Ridhoandika112/SPIKO-Sistem-Pakan-Ikan-Otomatis/3D Desain/Tampak Jauh.png

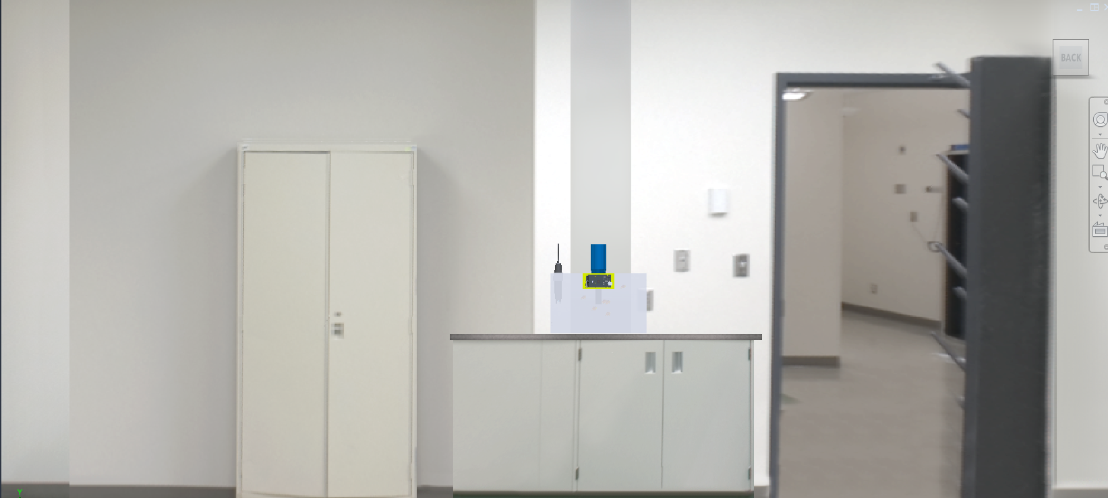
3D Desain/Tampak Jauh.png
